keiboard4200/SplitChoc64/hardware/main-pcb/Ver002/1_RIGHT/3dmodels/JST_S2B-PH-SM4-TB_KICAD_ALIGNED.step

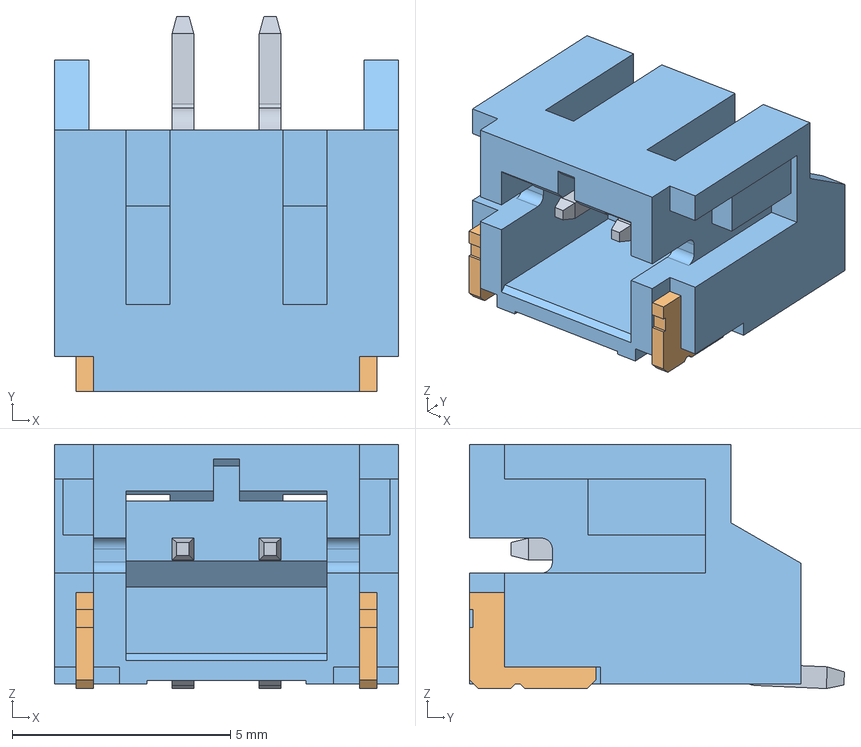
[picture p15: CAD file, 2026-08-27]
hardware/main-pcb/Ver002/1_RIGHT/3dmodels/JST_S2B-PH-SM4-TB_KICAD_ALIGNED.step
7.90 x 8.60 x 5.60 mm
