keiboard4200/SplitChoc64/hardware/main-pcb/Ver002/2_LEFT/3dmodels/R_0603_1608_PROXY.step

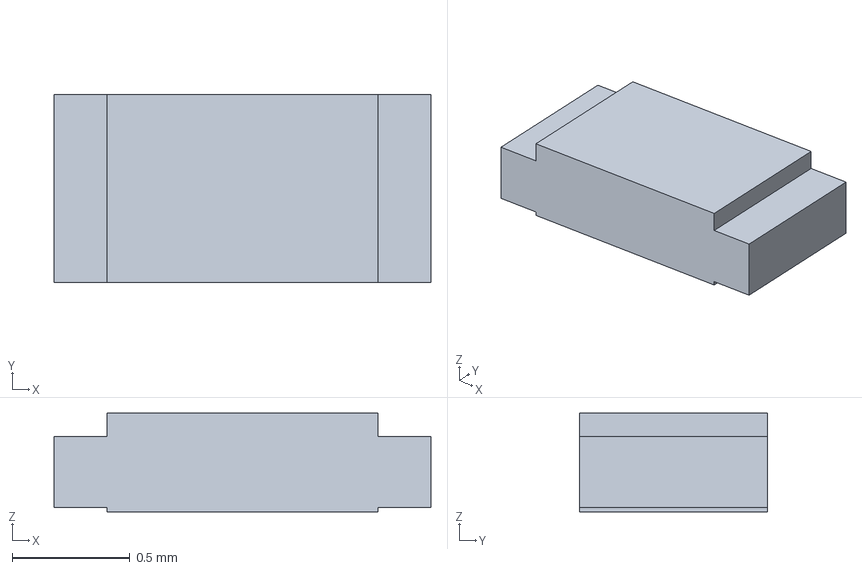
[picture p16: CAD file, 2026-08-27]
hardware/main-pcb/Ver002/2_LEFT/3dmodels/R_0603_1608_PROXY.step
1.60 x 0.8 x 0.42 mm
