keiboard4200/SplitChoc64/hardware/main-pcb/Ver002/4_CASE/SplitChoc64_VER001.005_RIGHT_BottomCase.step

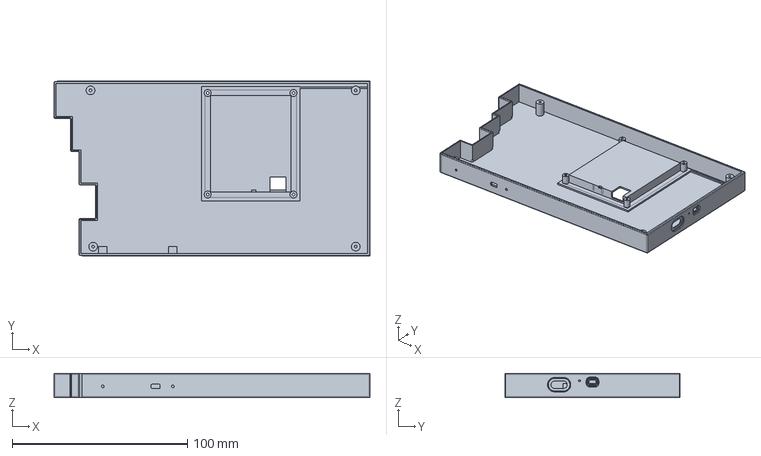
[picture p17: CAD file, 2026-08-31]
hardware/main-pcb/Ver002/4_CASE/SplitChoc64_VER001.005_RIGHT_BottomCase.step
180.5 x 100.2 x 13.8 mm
