keiboard4200/SplitChoc64/hardware/main-pcb/Ver002/4_CASE/SplitChoc64_VER001.006_LEFT_BottomCase.step

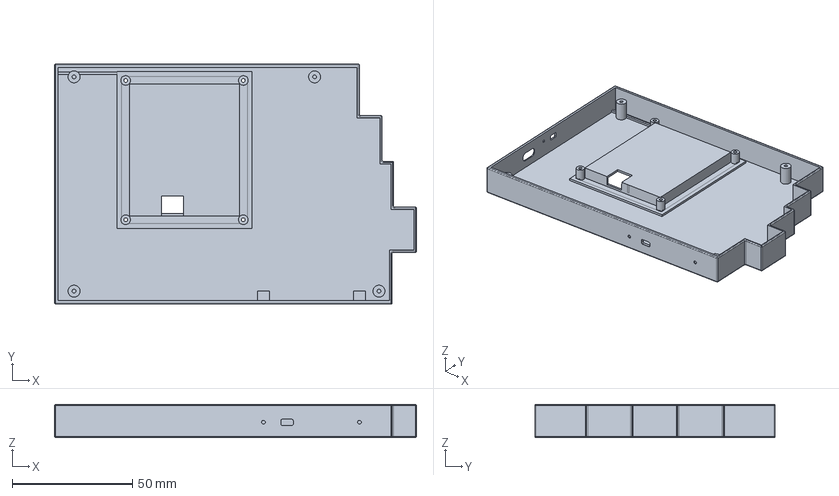
[picture p18: CAD file, 2026-08-31]
hardware/main-pcb/Ver002/4_CASE/SplitChoc64_VER001.006_LEFT_BottomCase.step
150.8 x 100.2 x 13.8 mm
