keiboard4200/SplitChoc64/hardware/main-pcb/Ver002/1_RIGHT/3dmodels/kailh_choc_socket.step

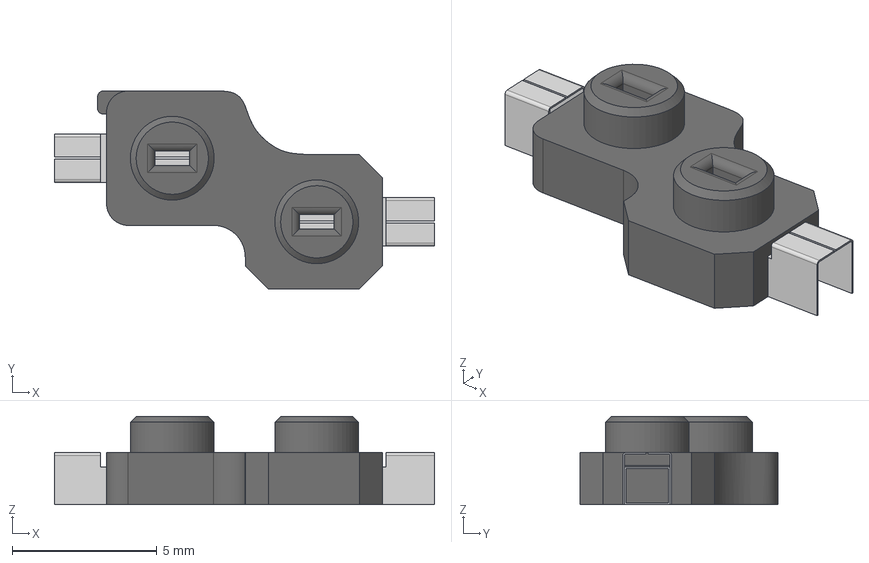
[picture p19: CAD file, 2026-08-24]
hardware/main-pcb/Ver002/1_RIGHT/3dmodels/kailh_choc_socket.step
13.1 x 6.85 x 3.05 mm
