keiboard4200/SplitChoc64/hardware/main-pcb/Ver002/2_LEFT/3dmodels/kailh_choc.step

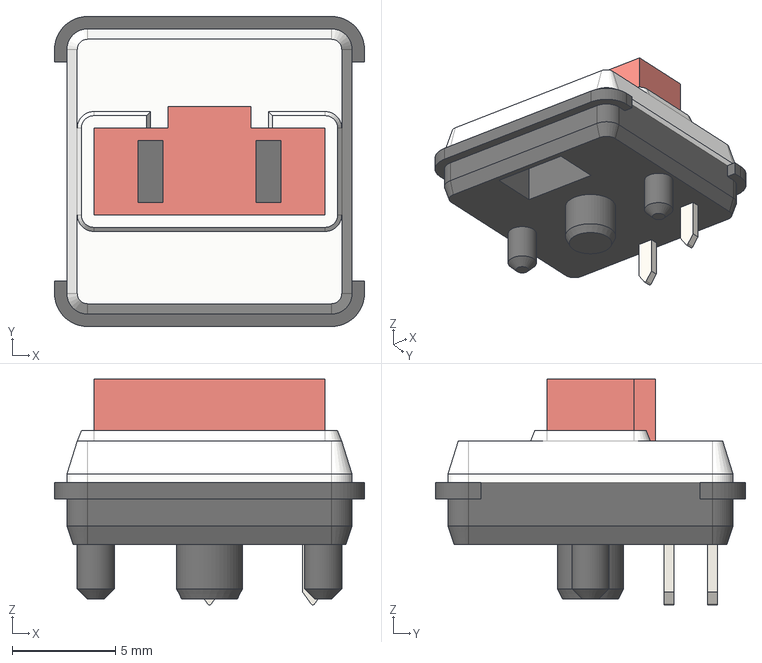
[picture p20: CAD file, 2026-08-24]
hardware/main-pcb/Ver002/2_LEFT/3dmodels/kailh_choc.step
15.0 x 15.0 x 10.9 mm
