keiboard4200/SplitChoc64/hardware/main-pcb/Ver002/4_CASE/ToraboTsuki_Trackball_Holder_19mm_Ver001.001.step

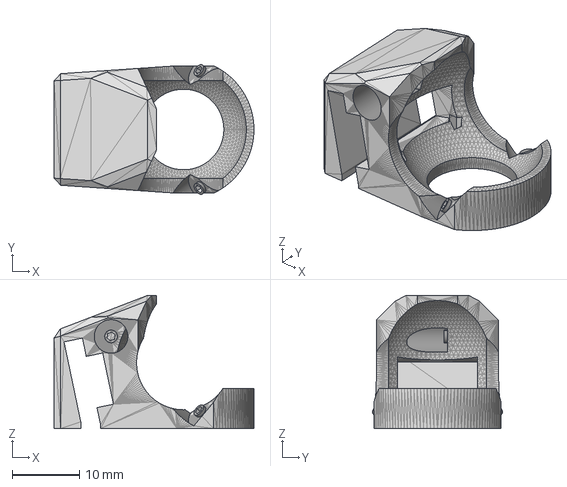
[picture p21: CAD file, 2026-08-24]
hardware/main-pcb/Ver002/4_CASE/ToraboTsuki_Trackball_Holder_19mm_Ver001.001.step
29.8 x 19.4 x 19.8 mm
